fablabromagna-org/christmas-sign/ATtiny3/Immagini/Dubbi2.png

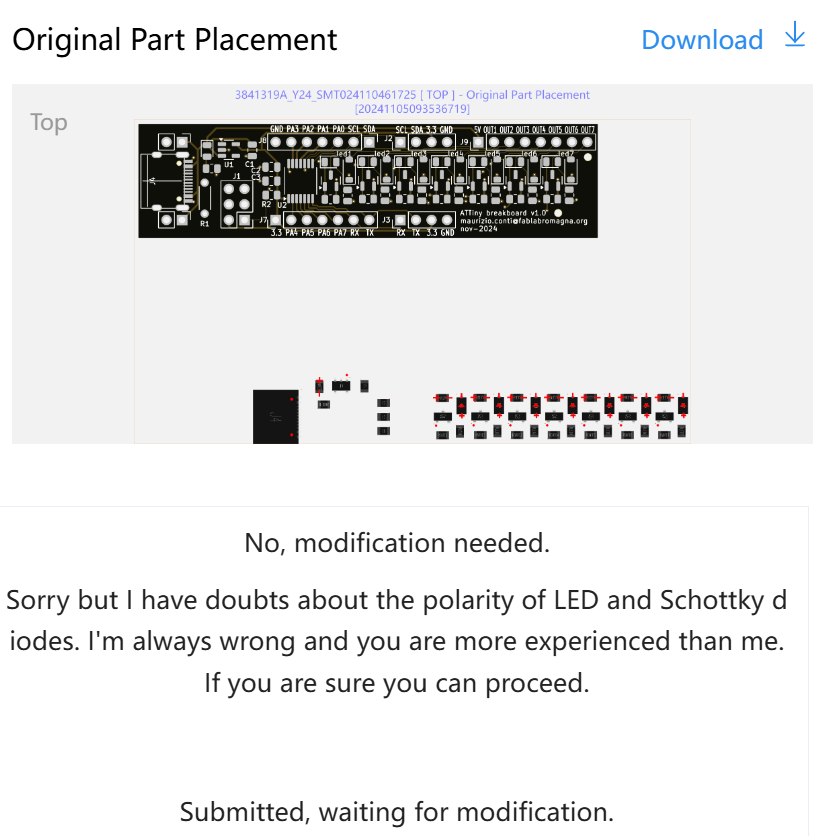
ATtiny3/Immagini/Dubbi2.png
